NorthernStars/sumoino/Sumorobot/examples/Drive_EE/Drive_EE.ino

// Sumoroboti servode juhtimine 
// EIK Robootikaklubi <http://robot.itcollege.ee> 
 
// lisame vajalikud teegid 
#include <Servo.h> 
#include <Sumo.h> 
 
void setup() 
{ 
  // initsialiseerime servo mootorid 
  start(); 
} 
 
// laseme robotil liikuda sekund edasi ja sekund tagasi xD 
// VIHJE: vahel tekib vajadus mootoreid juhtida eraldi, selleks kasuta 
//        vasakMootor(suund, kiirus) paremMootor(suund, speed) 
//        kus suund on EDASI voi TAGASI ja kiirus 0% kuni 100% 
//        (proovi: vasakMootor(EDASI, 55) paremMootor(TAGASI, MAX_KIIRUS) vasakMootor(EDASI, AEGLANE)) 
void loop() 
{ 
  edasi();            // anname suuna, kuhu liikuda 
  viivitus( SEKUND ); // liigume 1 sekund edasi 
  tagasi();           // anname suuna, kuhu liikuda 
  viivitus( SEKUND ); // liigume 1 sekund tagasi 
} 
 
